T76-org/drpd/docs/docs/internals/interactive-diagram.mdx

---
sidebar_position: 1
slug: /internals/interactive-diagram/
hide_table_of_contents: true
title: Interactive diagram
description: Explore the Dr. PD R2605-A schematics in KiCanvas.
---

import InteractiveDiagram from '@site/src/components/InteractiveDiagram';

# Interactive diagram

Explore the R2605-A schematics in [KiCanvas](https://kicanvas.org/). Pan and zoom the diagram, select components, and use the project panel to move between schematic sheets.

<InteractiveDiagram />
