T76-org/drpd/frontend/src/content/initialNotice3.md

## Start using Dr. PD

That's it! If this is your first time using Dr. PD, the application will prompt you to pair your device as soon as you close this message.

There is no need to install any drivers or other software. Dr. PD runs entirely in your web browser, and all of your settings and log data are stored locally on your device. 

A [Python library](https://github.com/T76-org/drpd/tree/main/python) and terminal-based client are also available if you want to interact with Dr. PD programmatically.

To learn more about Dr. PD's features and how to use them, please read our [user guide](https://t76.org/drpd/docs/).
