T76-org/drpd/docs/docs/programming-guide/using-python-library/reference/package.mdx

---
sidebar_position: 50
sidebar_label: Package Entry Points
---

# Package Entry Points

:::info[Generated reference]
This page is generated from the Python source under `python/t76`. Do not edit it by hand; update source docstrings or the generator instead.
:::

Top-level package modules and command-line entry helpers.

## `t76`

**Source:** `python/t76/__init__.py`

Python tooling for T76.org devices.

No public classes or functions defined directly in this module.
