T76-org/drpd/hardware/R2605-A/kicad-schematics/Analog Monitor.kicad_sch

## KiCad design hardware/R2605-A/kicad-schematics/Analog Monitor.kicad_sch (2026-07-29)

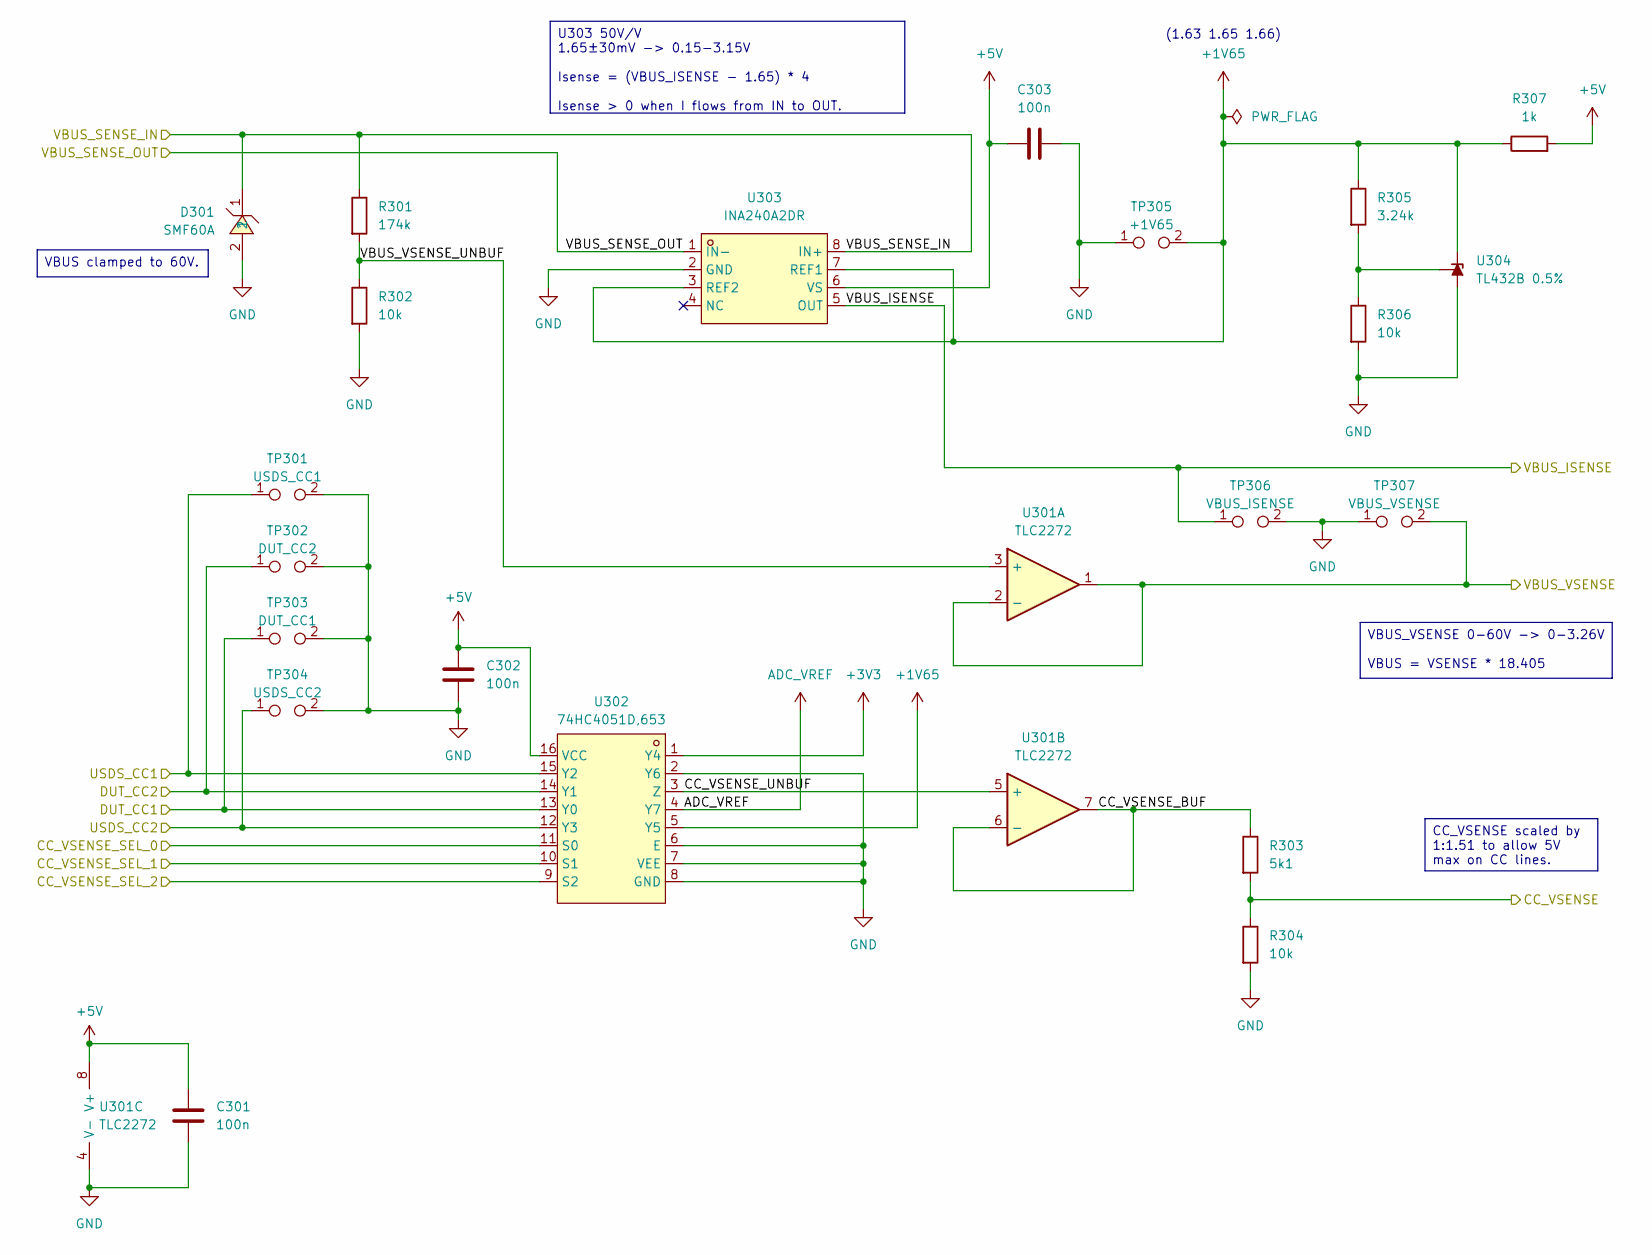
[picture p29: schematic Analog Monitor.kicad_sch]

Parts:
C301, C302, C303: 100n; C_1206_3216Metric; MPN C15008
D301: SMF60A; SOD-123FL_L2.8-W1.8-LS3.6-RD; LCSC Part C2857295
R301: 174k; R_1206_3216Metric; LCSC Part C274094
R302: 10k; R_1206_3216Metric; LCSC Part C17902
R303: 5k1; R_1206_3216Metric; MPN C26033
R304, R306: 10k; R_1206_3216Metric; MPN C17902
R305: 3.24k; R_1206_3216Metric; MPN C5153989
R307: 1k; R_1206_3216Metric; MPN C4410
TP301: USDS_CC1; TestPoint_2Pads_Pitch2.54mm_Drill0.8mm
TP302: DUT_CC2; TestPoint_2Pads_Pitch2.54mm_Drill0.8mm
TP303: DUT_CC1; TestPoint_2Pads_Pitch2.54mm_Drill0.8mm
TP304: USDS_CC2; TestPoint_2Pads_Pitch2.54mm_Drill0.8mm
TP305: +1V65; TestPoint_2Pads_Pitch2.54mm_Drill0.8mm
TP306: VBUS_ISENSE; TestPoint_2Pads_Pitch2.54mm_Drill0.8mm
TP307: VBUS_VSENSE; TestPoint_2Pads_Pitch2.54mm_Drill0.8mm
U301: TLC2272; SOIC-8_L4.9-W3.9-P1.27-LS6.0-BL; MPN C6979
U302: 74HC4051D,653; SOIC-16_L9.9-W3.9-P1.27-LS6.0-BL; LCSC Part C9386
U303: INA240A2DR; SOIC-8_L5.0-W4.0-P1.27-LS6.0-BL; LCSC Part C2060768
U304: TL432B 0.5%; SOT-23-3_L2.9-W1.3-P1.90-LS2.4-BR; LCSC Part C545558

Connections:
+1V65: R305.1, R307.1, TP305.2, U302.5 (Y5), U303.3 (REF2), U303.7 (REF1), U304.2 (K)
+3V3: U302.1 (Y4)
+5V: C301.1, C302.1, C303.1, R307.2, U301.8 (V+), U302.16 (VCC), U303.6 (VS)
ADC_VREF: U302.4 (Y7)
CC_VSENSE: R303.2, R304.1
CC_VSENSE_BUF: R303.1, U301.6 (-), U301.7
CC_VSENSE_SEL_0: U302.11 (S0)
CC_VSENSE_SEL_1: U302.10 (S1)
CC_VSENSE_SEL_2: U302.9 (S2)
CC_VSENSE_UNBUF: U301.5 (+), U302.3 (Z)
DUT_CC1: TP303.1, U302.13 (Y0)
DUT_CC2: TP302.1, U302.14 (Y1)
GND: C301.2, C302.2, C303.2, D301.2, R302.2, R304.2, R306.2, TP301.2, TP302.2, TP303.2, TP304.2, TP305.1, TP306.2, TP307.1, U301.4 (V-), U302.2 (Y6), U302.6 (E), U302.7 (VEE), U302.8 (GND), U303.2 (GND), U304.3 (A)
unnamed: R305.2, R306.1, U304.1 (REF)
USDS_CC1: TP301.1, U302.15 (Y2)
USDS_CC2: TP304.1, U302.12 (Y3)
VBUS_ISENSE: TP306.1, U303.5 (OUT)
VBUS_SENSE_IN: D301.1, R301.1, U303.8 (IN+)
VBUS_SENSE_OUT: U303.1 (IN-)
VBUS_VSENSE: TP307.2, U301.1, U301.2 (-)
VBUS_VSENSE_UNBUF: R301.2, R302.1, U301.3 (+)

Notes on the sheet:
(1.63 1.65 1.66)
VBUS clamped to 60V.
U303 50V/V 1.65±30mV -> 0.15-3.15V Isense = (VBUS_ISENSE - 1.65) * 4 Isense > 0 when I flows from IN to OUT.
CC_VSENSE scaled by 1:1.51 to allow 5V max on CC lines.
VBUS_VSENSE 0-60V -> 0-3.26V VBUS = VSENSE * 18.405
