T76-org/drpd/hardware/R2605-A/kicad-schematics/Bus Connector and Digital IO.kicad_sch

## KiCad design hardware/R2605-A/kicad-schematics/Bus Connector and Digital IO.kicad_sch (2026-07-29)

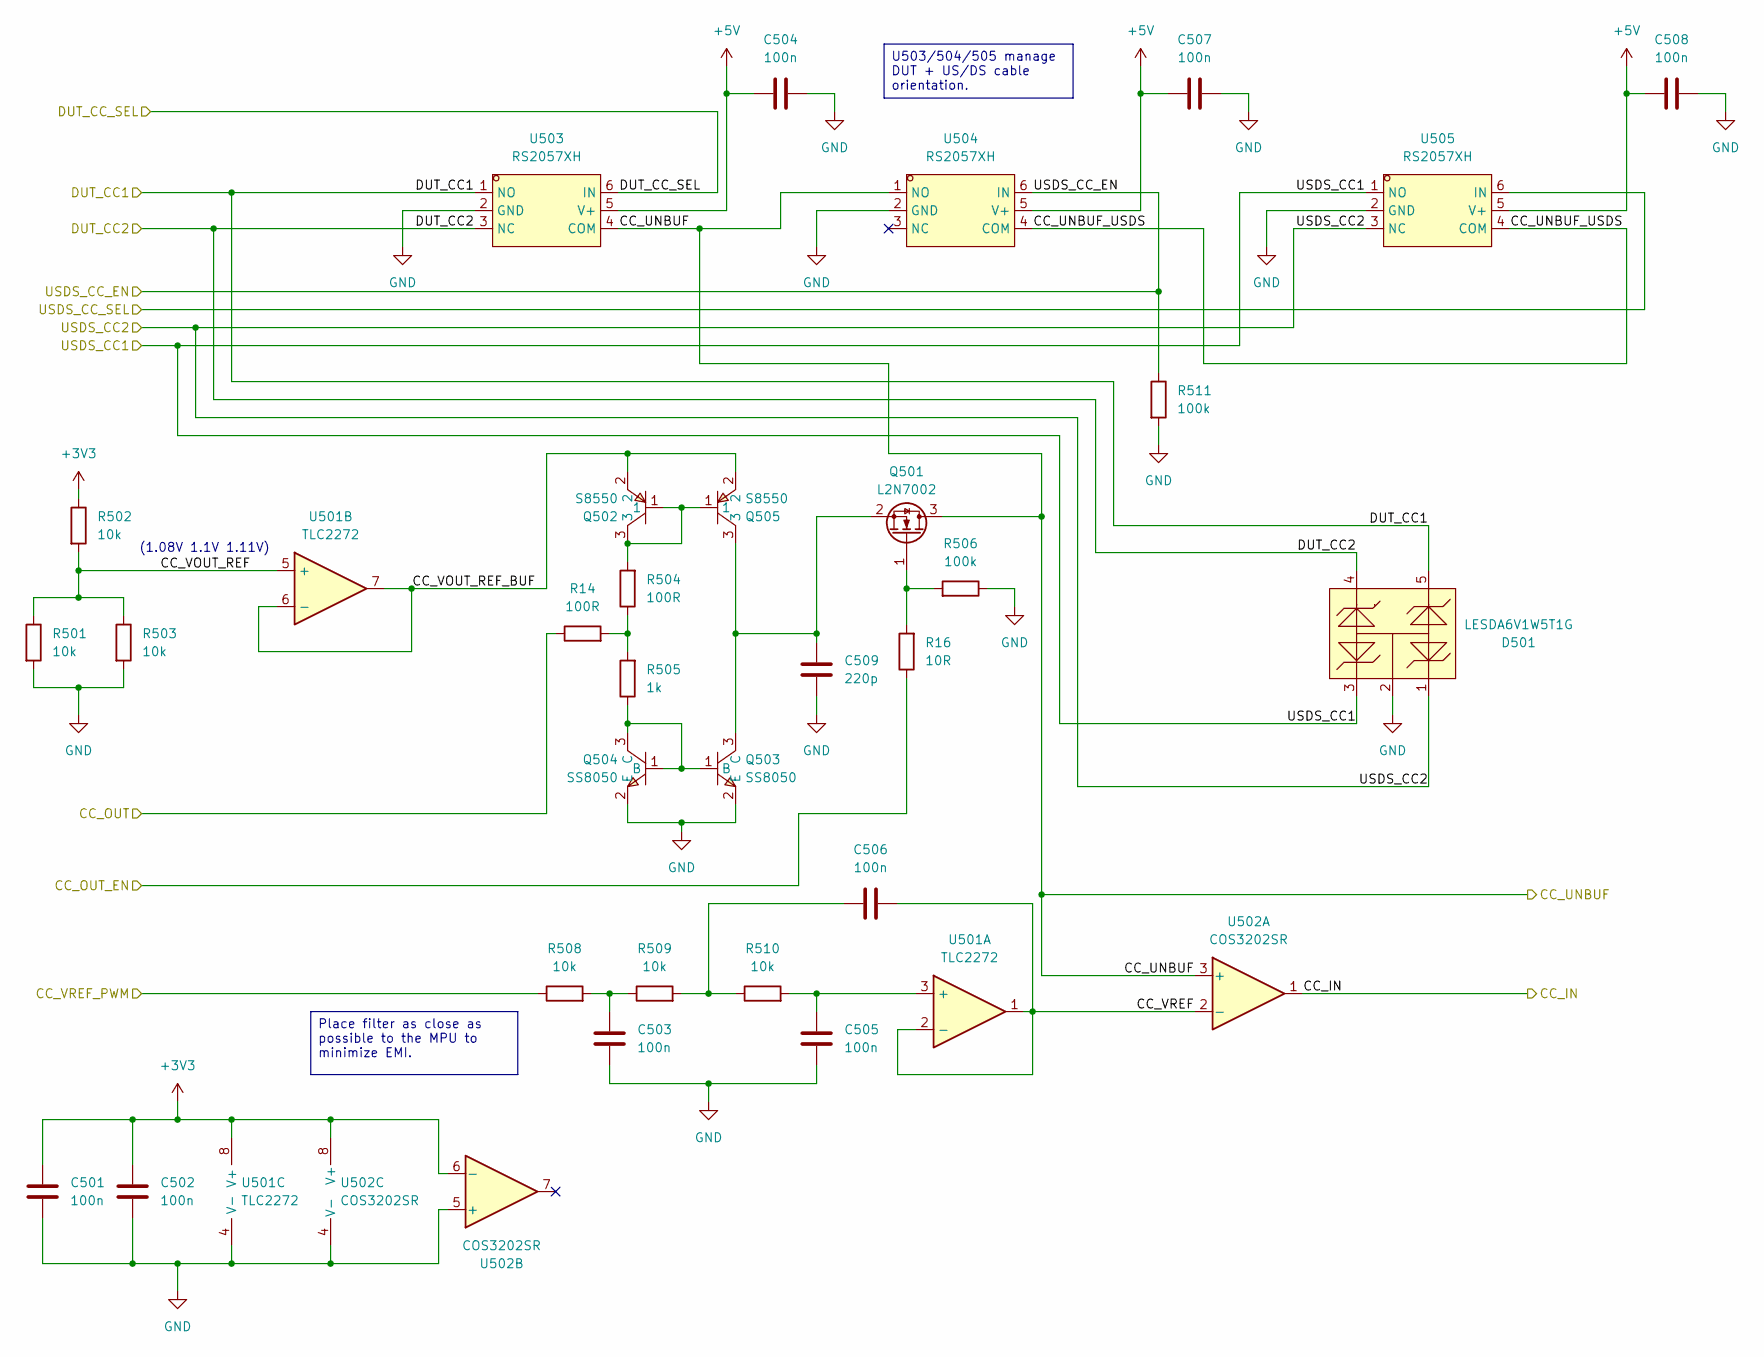
[picture p30: schematic Bus Connector and Digital IO.kicad_sch]

Parts:
C501, C502, C503, C504, C505, C506, C507, C508: 100n; C_1206_3216Metric; MPN C15008
C509: 220p; C_1206_3216Metric; MPN C107175
D501: LESDA6V1W5T1G; SC-88A_L2.0-W1.3-P0.65-LS2.1-BL-1; LCSC Part C383221
Q501: L2N7002; SOT-23-3_L3.0-W1.7-P0.95-LS2.9-BR; LCSC Part C22446827
Q502, Q505: S8550; SOT-23-3_L2.9-W1.6-P1.90-LS2.8-BR; MPN S8550(RANGE:120-200); LCSC Part C105432
Q503, Q504: SS8050; SOT-23-3_L2.9-W1.3-P1.90-LS2.4-BR; MPN SS8050(RANGE:200-350); LCSC Part C2150
R14, R504: 100R; R_1206_3216Metric; MPN C17901
R16: 10R; R_1206_3216Metric; MPN C17903
R501, R502, R503, R508, R509, R510: 10k; R_1206_3216Metric; MPN C17902
R505: 1k; R_1206_3216Metric; MPN C4410
R506, R511: 100k; R_1206_3216Metric; MPN C17900
U501: TLC2272; SOIC-8_L4.9-W3.9-P1.27-LS6.0-BL; MPN C6979
U502: COS3202SR; SOIC-8_L5.0-W4.0-P1.27-LS6.0-BL; MPN C49304671
U503, U504, U505: RS2057XH; SOT-23-6_L2.9-W1.6-P0.95-LS2.8-BR; LCSC Part C255474

Connections:
+3V3: C501.1, C502.1, R502.1, U501.8 (V+), U502.6 (-), U502.8 (V+)
+5V: C504.2, C507.2, C508.2, U503.5 (V+), U504.5 (V+), U505.5 (V+)
CC_IN: U502.1
CC_OUT: R14.1
CC_OUT_EN: R16.1
CC_UNBUF: Q501.3 (D), U502.3 (+), U503.4 (COM), U504.1 (NO)
CC_UNBUF_USDS: U504.4 (COM), U505.4 (COM)
CC_VOUT_REF: R501.1, R502.2, R503.1, U501.5 (+)
CC_VOUT_REF_BUF: Q502.2, Q505.2, U501.6 (-), U501.7
CC_VREF: C506.2, U501.1, U501.2 (-), U502.2 (-)
CC_VREF_PWM: R508.1
DUT_CC1: D501.5, U503.1 (NO)
DUT_CC2: D501.4, U503.3 (NC)
DUT_CC_SEL: U503.6 (IN)
GND: C501.2, C502.2, C503.2, C504.1, C505.2, C507.1, C508.1, C509.2, D501.2, Q503.2 (E), Q504.2 (E), R501.2, R503.2, R506.1, R511.2, U501.4 (V-), U502.4 (V-), U502.5 (+), U503.2 (GND), U504.2 (GND), U505.2 (GND)
unnamed: C503.1, R508.2, R509.1
unnamed: C505.1, R510.2, U501.3 (+)
unnamed: C506.1, R509.2, R510.1
unnamed: C509.1, Q501.2 (S), Q503.3 (C), Q505.3
unnamed: Q501.1 (G), R16.2, R506.2
unnamed: Q502.1, Q502.3, Q505.1, R504.2
unnamed: Q503.1 (B), Q504.1 (B), Q504.3 (C), R505.1
unnamed: R14.2, R504.1, R505.2
USDS_CC1: D501.3, U505.1 (NO)
USDS_CC2: D501.1, U505.3 (NC)
USDS_CC_EN: R511.1, U504.6 (IN)
USDS_CC_SEL: U505.6 (IN)

Notes on the sheet:
(1.08V 1.1V 1.11V)
Place filter as close as possible to the MPU to minimize EMI.
U503/504/505 manage DUT + US/DS cable orientation.
