T76-org/drpd/hardware/R2605-A/kicad-schematics/Digital Control.kicad_sch

## KiCad design hardware/R2605-A/kicad-schematics/Digital Control.kicad_sch (2026-07-29)

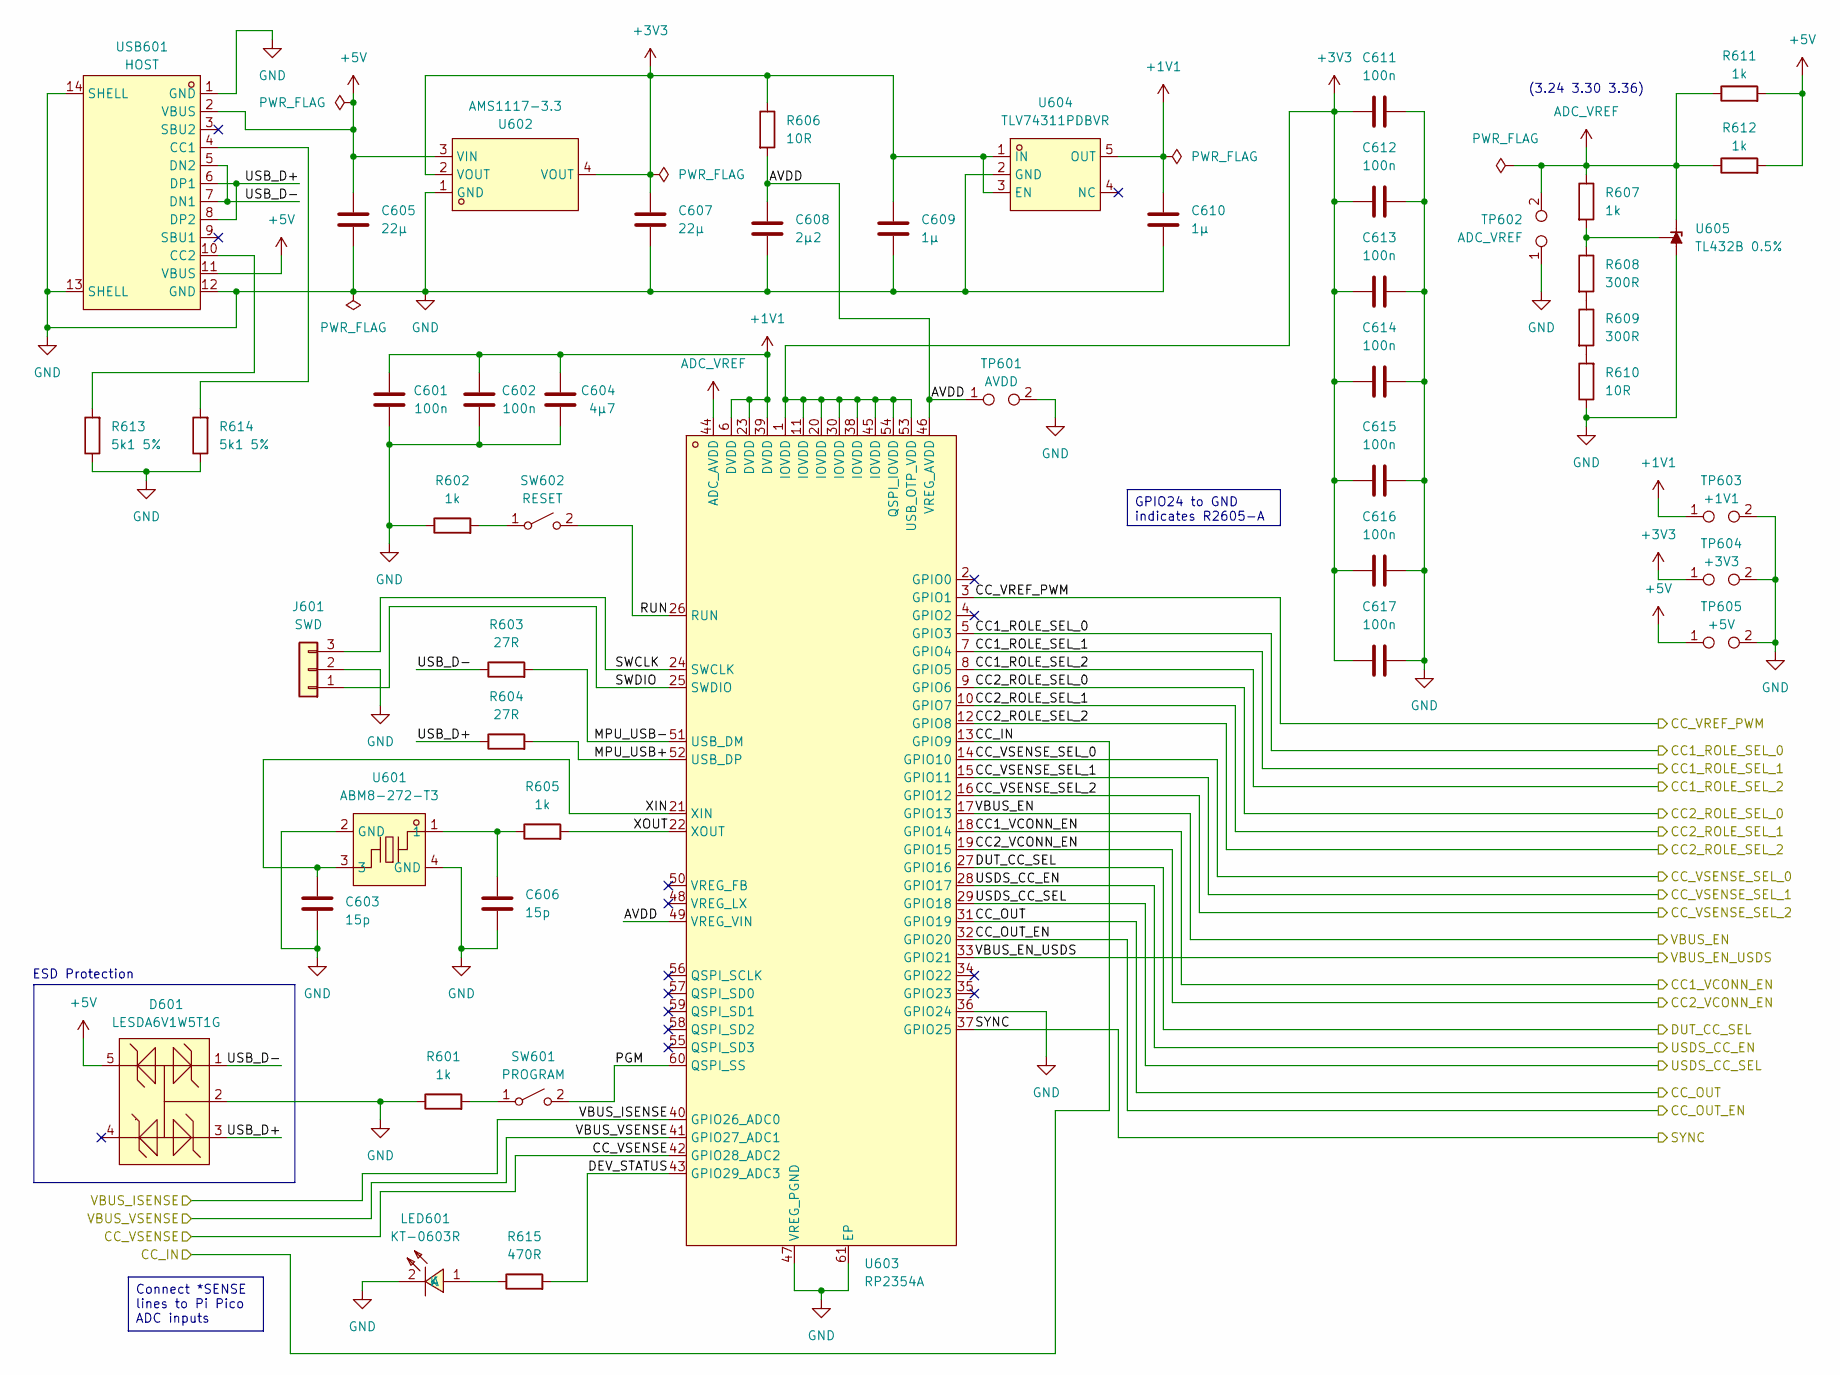
[picture p31: schematic Digital Control.kicad_sch]

Parts:
C601, C602, C611, C612, C613, C614, C615, C616, C617: 100n; C_1206_3216Metric; MPN C15008
C603, C606: 15p; C_1206_3216Metric; MPN C326650
C604: 4µ7; C_1206_3216Metric; MPN C29823
C605, C607: 22µ; C_1206_3216Metric; MPN C12891
C608: 2µ2; C_1206_3216Metric; MPN C50254
C609, C610: 1µ; C_1206_3216Metric; MPN C1848
D601: LESDA6V1W5T1G; SC-88A_L2.0-W1.3-P0.65-LS2.1-BL-1; LCSC Part C383221
J601: SWD; PinSocket_1x03_P2.54mm_Vertical
LED601: KT-0603R; LED-SMD_L1.6-W0.8-R-RD; MPN KT-0603R; LCSC Part C2286
R601, R602, R605, R607, R611, R612: 1k; R_1206_3216Metric; MPN C4410
R603, R604: 27R; R_1206_3216Metric; MPN C2933656
R606, R610: 10R; R_1206_3216Metric; MPN C17903
R608, R609: 300R; R_1206_3216Metric; MPN C17887
R613, R614: 5k1 5%; R_1206_3216Metric; MPN C2907509
R615: 470R; R_1206_3216Metric; MPN C185720
SW601: PROGRAM; SW-SMD_L3.9-W3.0-P4.45; MPN C720477
SW602: RESET; SW-SMD_L3.9-W3.0-P4.45; MPN C720477
TP601: AVDD; TestPoint_2Pads_Pitch2.54mm_Drill0.8mm
TP602: ADC_VREF; TestPoint_2Pads_Pitch2.54mm_Drill0.8mm
TP603: +1V1; TestPoint_2Pads_Pitch2.54mm_Drill0.8mm
TP604: +3V3; TestPoint_2Pads_Pitch2.54mm_Drill0.8mm
TP605: +5V; TestPoint_2Pads_Pitch2.54mm_Drill0.8mm
U601: ABM8-272-T3; CRYSTAL-SMD_4P-L3.2-W2.5-BL; LCSC Part C20625731
U602: AMS1117-3.3; SOT-223-3_L6.5-W3.4-P2.30-LS7.0-BR; LCSC Part C6186
U603: RP2354A; QFN-60_L7.0-W7.0-P0.40-TL-EP3.4; LCSC Part C41378174
U604: TLV74311PDBVR; SOT-23-5_L3.0-W1.7-P0.95-LS2.8-BL; LCSC Part C485147
U605: TL432B 0.5%; SOT-23-3_L2.9-W1.3-P1.90-LS2.4-BR; LCSC Part C545558
USB601: HOST; USB-C-SMD_TYPE-C-6PIN-2MD-073; LCSC Part C2765186

Connections:
+1V1: C601.1, C602.1, C604.1, C610.1, TP603.1, U603.6 (DVDD), U603.23 (DVDD), U603.39 (DVDD), U604.5 (OUT)
+3V3: C607.1, C609.1, C611.1, C612.1, C613.1, C614.1, C615.1, C616.1, C617.1, R606.1, TP604.1, U602.2 (VOUT), U602.4 (VOUT), U603.1 (IOVDD), U603.11 (IOVDD), U603.20 (IOVDD), U603.30 (IOVDD), U603.38 (IOVDD), U603.45 (IOVDD), U603.53 (USB_OTP_VDD), U603.54 (QSPI_IOVDD), U604.1 (IN), U604.3 (EN)
+5V: C605.1, D601.5, R611.2, R612.2, TP605.1, U602.3 (VIN), USB601.2 (VBUS), USB601.11 (VBUS)
ADC_VREF: R607.1, R611.1, R612.1, TP602.2, U603.44 (ADC_AVDD), U605.2 (K)
AVDD: C608.1, R606.2, TP601.1, U603.46 (VREG_AVDD), U603.49 (VREG_VIN)
CC1_ROLE_SEL_0: U603.5 (GPIO3)
CC1_ROLE_SEL_1: U603.7 (GPIO4)
CC1_ROLE_SEL_2: U603.8 (GPIO5)
CC1_VCONN_EN: U603.18 (GPIO14)
CC2_ROLE_SEL_0: U603.9 (GPIO6)
CC2_ROLE_SEL_1: U603.10 (GPIO7)
CC2_ROLE_SEL_2: U603.12 (GPIO8)
CC2_VCONN_EN: U603.19 (GPIO15)
CC_IN: U603.13 (GPIO9)
CC_OUT: U603.31 (GPIO19)
CC_OUT_EN: U603.32 (GPIO20)
CC_VREF_PWM: U603.3 (GPIO1)
CC_VSENSE: U603.42 (GPIO28_ADC2)
CC_VSENSE_SEL_0: U603.14 (GPIO10)
CC_VSENSE_SEL_1: U603.15 (GPIO11)
CC_VSENSE_SEL_2: U603.16 (GPIO12)
DEV_STATUS: R615.2, U603.43 (GPIO29_ADC3)
DUT_CC_SEL: U603.27 (GPIO16)
GND: C601.2, C602.2, C603.2, C604.2, C605.2, C606.2, C607.2, C608.2, C609.2, C610.2, C611.2, C612.2, C613.2, C614.2, C615.2, C616.2, C617.2, D601.2, J601.2, LED601.2 (K), R601.1, R602.1, R610.1, R613.1, R614.1, TP601.2, TP602.1, TP603.2, TP604.2, TP605.2, U601.2 (GND), U601.4 (GND), U602.1 (GND), U603.36 (GPIO24), U603.47 (VREG_PGND), U603.61 (EP), U604.2 (GND), U605.3 (A), USB601.1 (GND), USB601.12 (GND), USB601.13 (SHELL), USB601.14 (SHELL)
MPU_USB+: R604.2, U603.52 (USB_DP)
MPU_USB-: R603.2, U603.51 (USB_DM)
unnamed: C606.1, R605.1, U601.1
unnamed: LED601.1 (A), R615.1
unnamed: R601.2, SW601.1 (A)
unnamed: R602.2, SW602.1 (A)
unnamed: R607.2, R608.1, U605.1 (REF)
unnamed: R608.2, R609.1
unnamed: R609.2, R610.2
unnamed: R613.2, USB601.10 (CC2)
unnamed: R614.2, USB601.4 (CC1)
PGM: SW601.2 (B), U603.60 (QSPI_SS)
RUN: SW602.2 (B), U603.26 (RUN)
SWCLK: J601.3, U603.24 (SWCLK)
SWDIO: J601.1, U603.25 (SWDIO)
SYNC: U603.37 (GPIO25)
USB_D+: D601.3, R604.1, USB601.6 (DP1), USB601.8 (DP2)
USB_D-: D601.1, R603.1, USB601.5 (DN2), USB601.7 (DN1)
USDS_CC_EN: U603.28 (GPIO17)
USDS_CC_SEL: U603.29 (GPIO18)
VBUS_EN: U603.17 (GPIO13)
VBUS_EN_USDS: U603.33 (GPIO21)
VBUS_ISENSE: U603.40 (GPIO26_ADC0)
VBUS_VSENSE: U603.41 (GPIO27_ADC1)
XIN: C603.1, U601.3, U603.21 (XIN)
XOUT: R605.2, U603.22 (XOUT)

Notes on the sheet:
ESD Protection
(3.24 3.30 3.36)
GPIO24 to GND indicates R2605-A
Connect *SENSE lines to Pi Pico ADC inputs
