T76-org/drpd/hardware/R2605-A/kicad-schematics/Dr.PD.kicad_sch

## KiCad design hardware/R2605-A/kicad-schematics/Dr.PD.kicad_sch (2026-07-29)

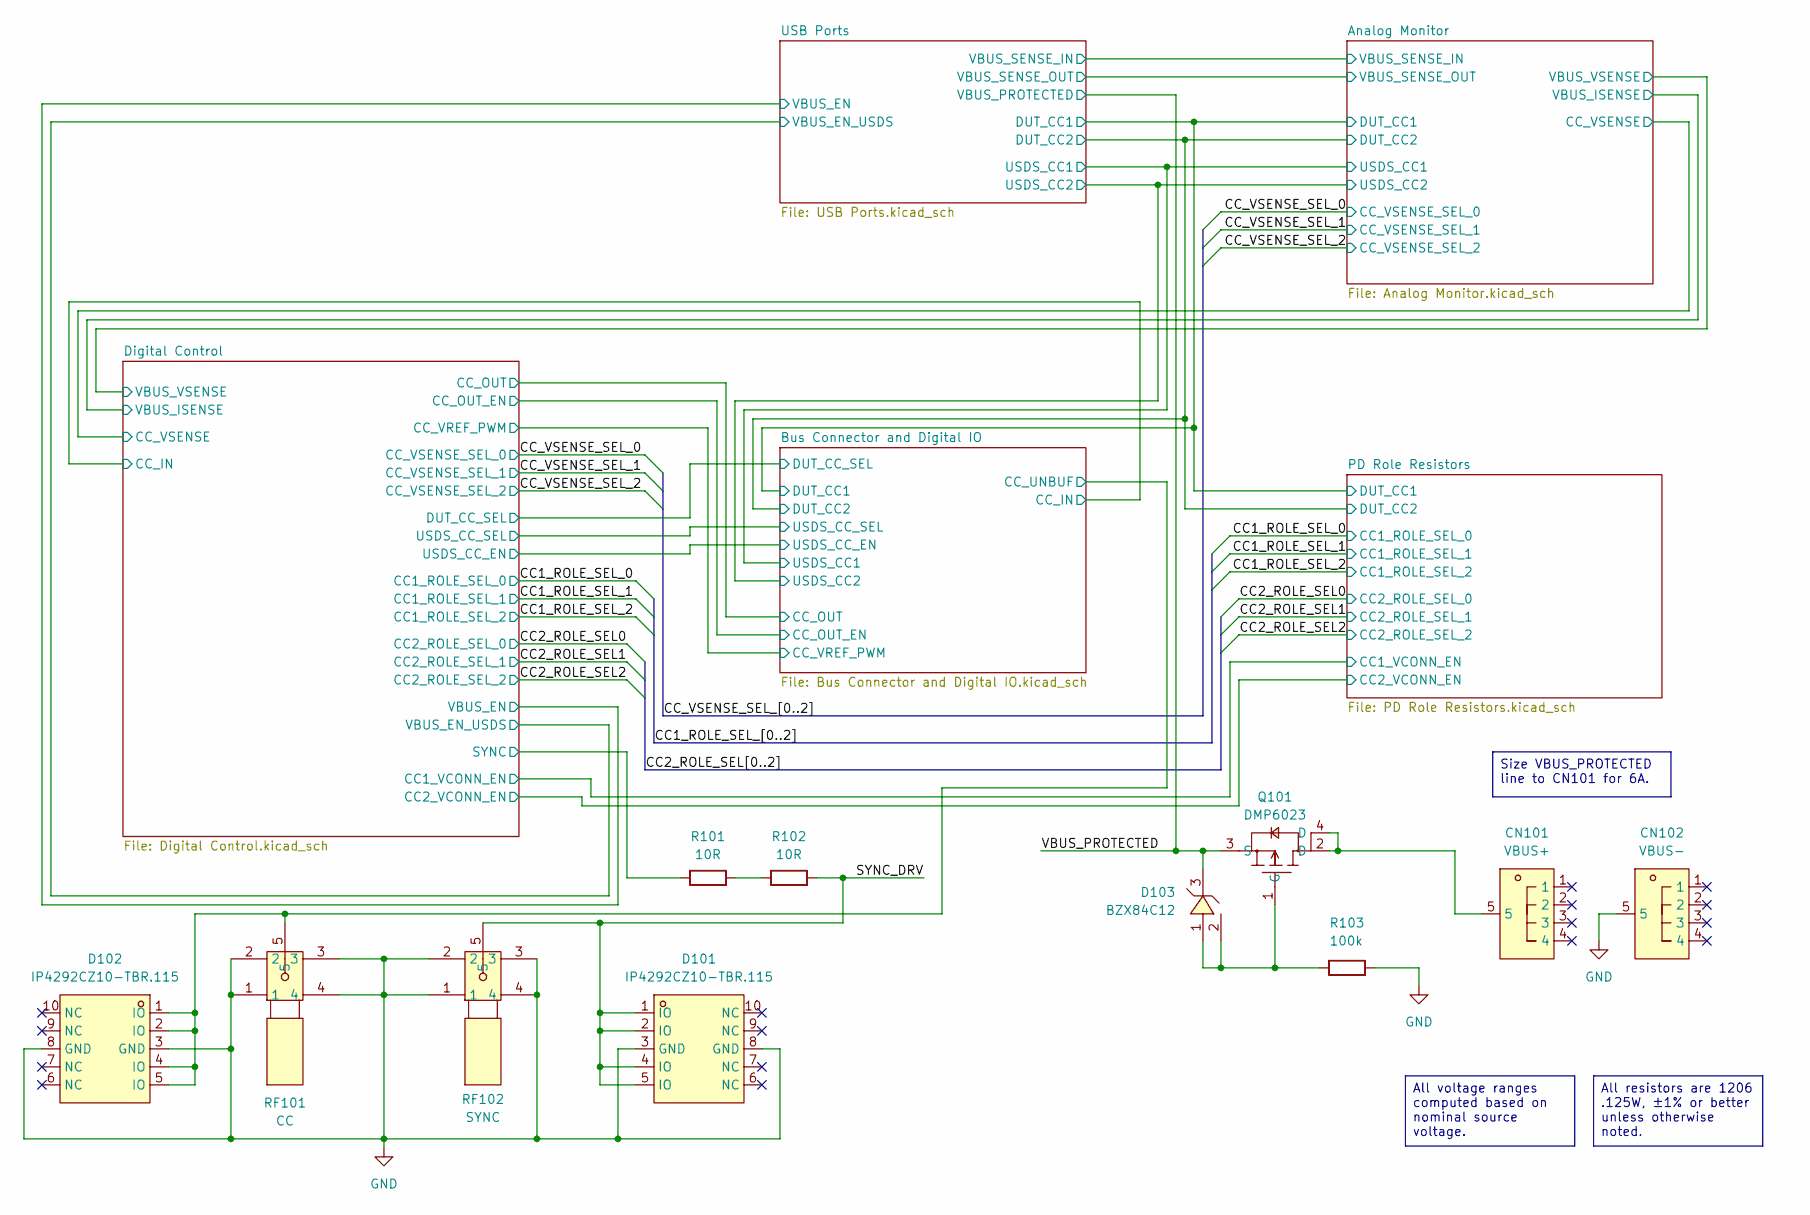
[picture p32: schematic Dr.PD.kicad_sch]

Parts:
CN101: VBUS+; ANT-TH_L33.0-W12.0_RED; LCSC Part C7437326
CN102: VBUS-; ANT-TH_L33.0-W12.0_BLACK; LCSC Part C7437327
D101, D102: IP4292CZ10-TBR.115; DFN2510A-10_L2.5-W1.0-P0.50-BL; LCSC Part C39832202
D103: BZX84C12; SOT-23_L2.9-W1.3-P1.90-LS2.4-BR; LCSC Part C19077471
Q101: DMP6023; SOT-223-4_L6.5-W3.5-P2.30-LS7.0-BR; LCSC Part C154901
R101, R102: 10R; R_1206_3216Metric; MPN C17903
R103: 100k; R_1206_3216Metric; MPN C17900
RF101: CC; BNC-TH_DOSIN-801-0051; LCSC Part C521210
RF102: SYNC; BNC-TH_DOSIN-801-0051; LCSC Part C521210

Connections:
CC_UNBUF: D102.1 (IO), D102.2 (IO), D102.4 (IO), D102.5 (IO), RF101.5
GND: CN102.5, D101.3 (GND), D101.8 (GND), D102.3 (GND), D102.8 (GND), R103.2, RF101.1, RF101.2, RF101.3, RF101.4, RF102.1, RF102.2, RF102.3, RF102.4
unnamed: CN101.5, Q101.2 (D), Q101.4 (D)
unnamed: D103.1, D103.2, Q101.1 (G), R103.1
unnamed: R101.2, R102.1
SYNC: R101.1
SYNC_DRV: D101.1 (IO), D101.2 (IO), D101.4 (IO), D101.5 (IO), R102.2, RF102.5
VBUS_PROTECTED: D103.3, Q101.3 (S)

Notes on the sheet:
Size VBUS_PROTECTED line to CN101 for 6A.
All voltage ranges computed based on nominal source voltage.
All resistors are 1206 .125W, ±1% or better unless otherwise noted.
