T76-org/drpd/hardware/R2605-A/kicad-schematics/PD Role Resistors.kicad_sch

## KiCad design hardware/R2605-A/kicad-schematics/PD Role Resistors.kicad_sch (2026-07-29)

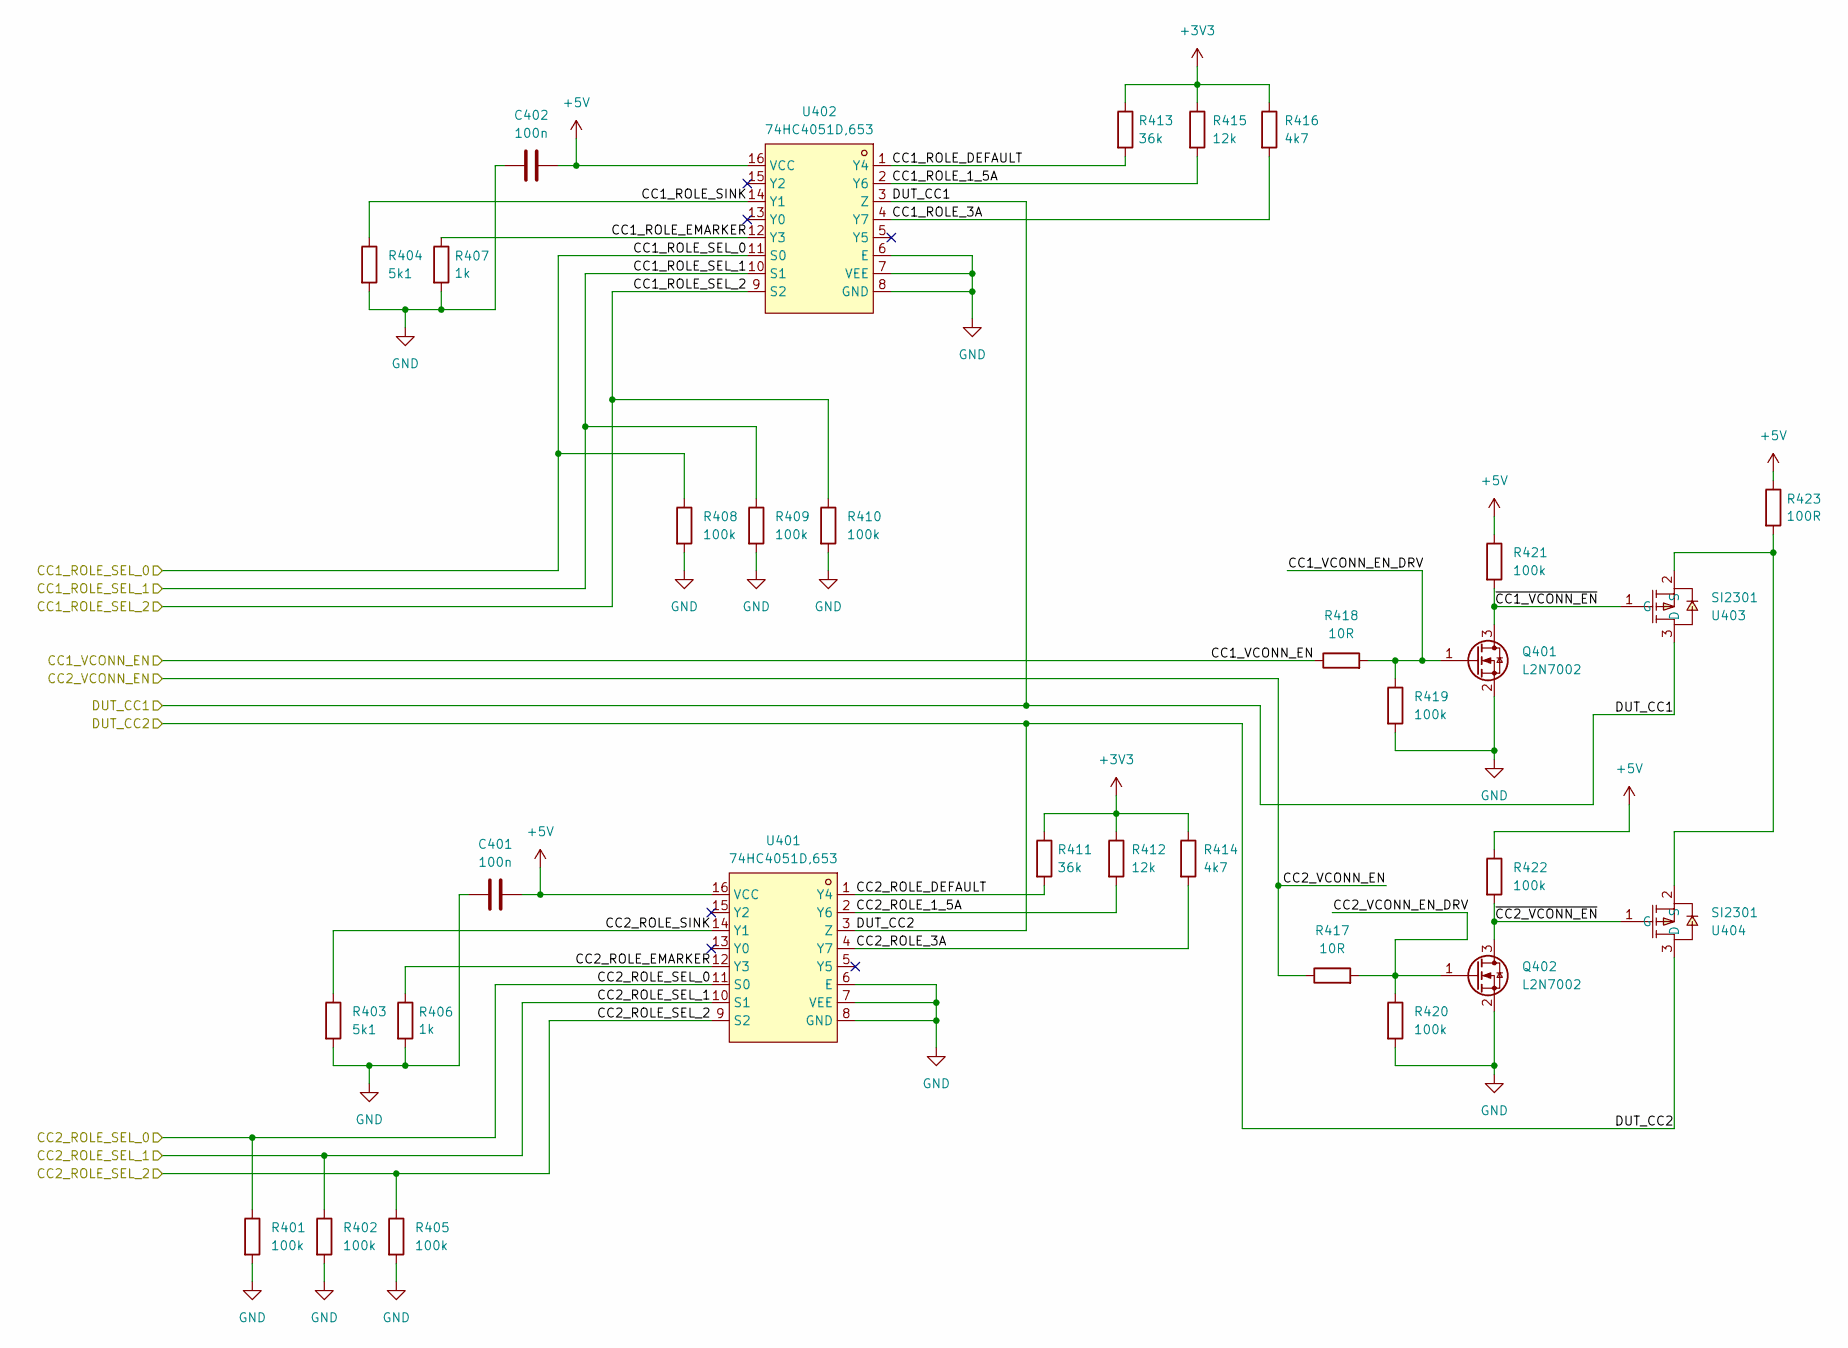
[picture p33: schematic PD Role Resistors.kicad_sch]

Parts:
C401, C402: 100n; C_1206_3216Metric; MPN C15008
Q401, Q402: L2N7002; SOT-23-3_L3.0-W1.7-P0.95-LS2.9-BR; LCSC Part C22446827
R401, R402, R405, R408, R409, R410, R419, R420, R421, R422: 100k; R_1206_3216Metric; MPN C17900
R403, R404: 5k1; R_1206_3216Metric; MPN C26033
R406, R407: 1k; R_1206_3216Metric; MPN C4410
R411, R413: 36k; R_1206_3216Metric; MPN C2933685
R412, R415: 12k; R_1206_3216Metric; MPN C17912
R414, R416: 4k7; R_1206_3216Metric; MPN C17936
R417, R418: 10R; R_1206_3216Metric; MPN C17903
R423: 100R; R_1206_3216Metric; MPN C17901
U401, U402: 74HC4051D,653; SOIC-16_L9.9-W3.9-P1.27-LS6.0-BL; LCSC Part C9386
U403, U404: SI2301; SOT-23-3_L2.9-W1.3-P1.90-LS2.4-BR; LCSC Part C5261052

Connections:
+3V3: R411.1, R412.1, R413.1, R414.1, R415.1, R416.1
+5V: C401.2, C402.2, R421.1, R422.1, R423.1, U401.16 (VCC), U402.16 (VCC)
CC1_ROLE_1_5A: R415.2, U402.2 (Y6)
CC1_ROLE_3A: R416.2, U402.4 (Y7)
CC1_ROLE_DEFAULT: R413.2, U402.1 (Y4)
CC1_ROLE_EMARKER: R407.1, U402.12 (Y3)
CC1_ROLE_SEL_0: R408.1, U402.11 (S0)
CC1_ROLE_SEL_1: R409.1, U402.10 (S1)
CC1_ROLE_SEL_2: R410.1, U402.9 (S2)
CC1_ROLE_SINK: R404.1, U402.14 (Y1)
CC1_VCONN_EN: R418.1
CC1_VCONN_EN_DRV: Q401.1 (G), R418.2, R419.1
CC2_ROLE_1_5A: R412.2, U401.2 (Y6)
CC2_ROLE_3A: R414.2, U401.4 (Y7)
CC2_ROLE_DEFAULT: R411.2, U401.1 (Y4)
CC2_ROLE_EMARKER: R406.1, U401.12 (Y3)
CC2_ROLE_SEL_0: R401.1, U401.11 (S0)
CC2_ROLE_SEL_1: R402.1, U401.10 (S1)
CC2_ROLE_SEL_2: R405.1, U401.9 (S2)
CC2_ROLE_SINK: R403.1, U401.14 (Y1)
CC2_VCONN_EN: R417.1
CC2_VCONN_EN_DRV: Q402.1 (G), R417.2, R420.1
DUT_CC1: U402.3 (Z), U403.3 (D)
DUT_CC2: U401.3 (Z), U404.3 (D)
GND: C401.1, C402.1, Q401.2 (S), Q402.2 (S), R401.2, R402.2, R403.2, R404.2, R405.2, R406.2, R407.2, R408.2, R409.2, R410.2, R419.2, R420.2, U401.6 (E), U401.7 (VEE), U401.8 (GND), U402.6 (E), U402.7 (VEE), U402.8 (GND)
unnamed: R423.2, U403.2 (S), U404.2 (S)
~CC1_VCONN_EN: Q401.3 (D), R421.2, U403.1 (G)
~CC2_VCONN_EN: Q402.3 (D), R422.2, U404.1 (G)
