T76-org/drpd/hardware/R2605-A/kicad-schematics/USB Ports.kicad_sch

## KiCad design hardware/R2605-A/kicad-schematics/USB Ports.kicad_sch (2026-07-29)

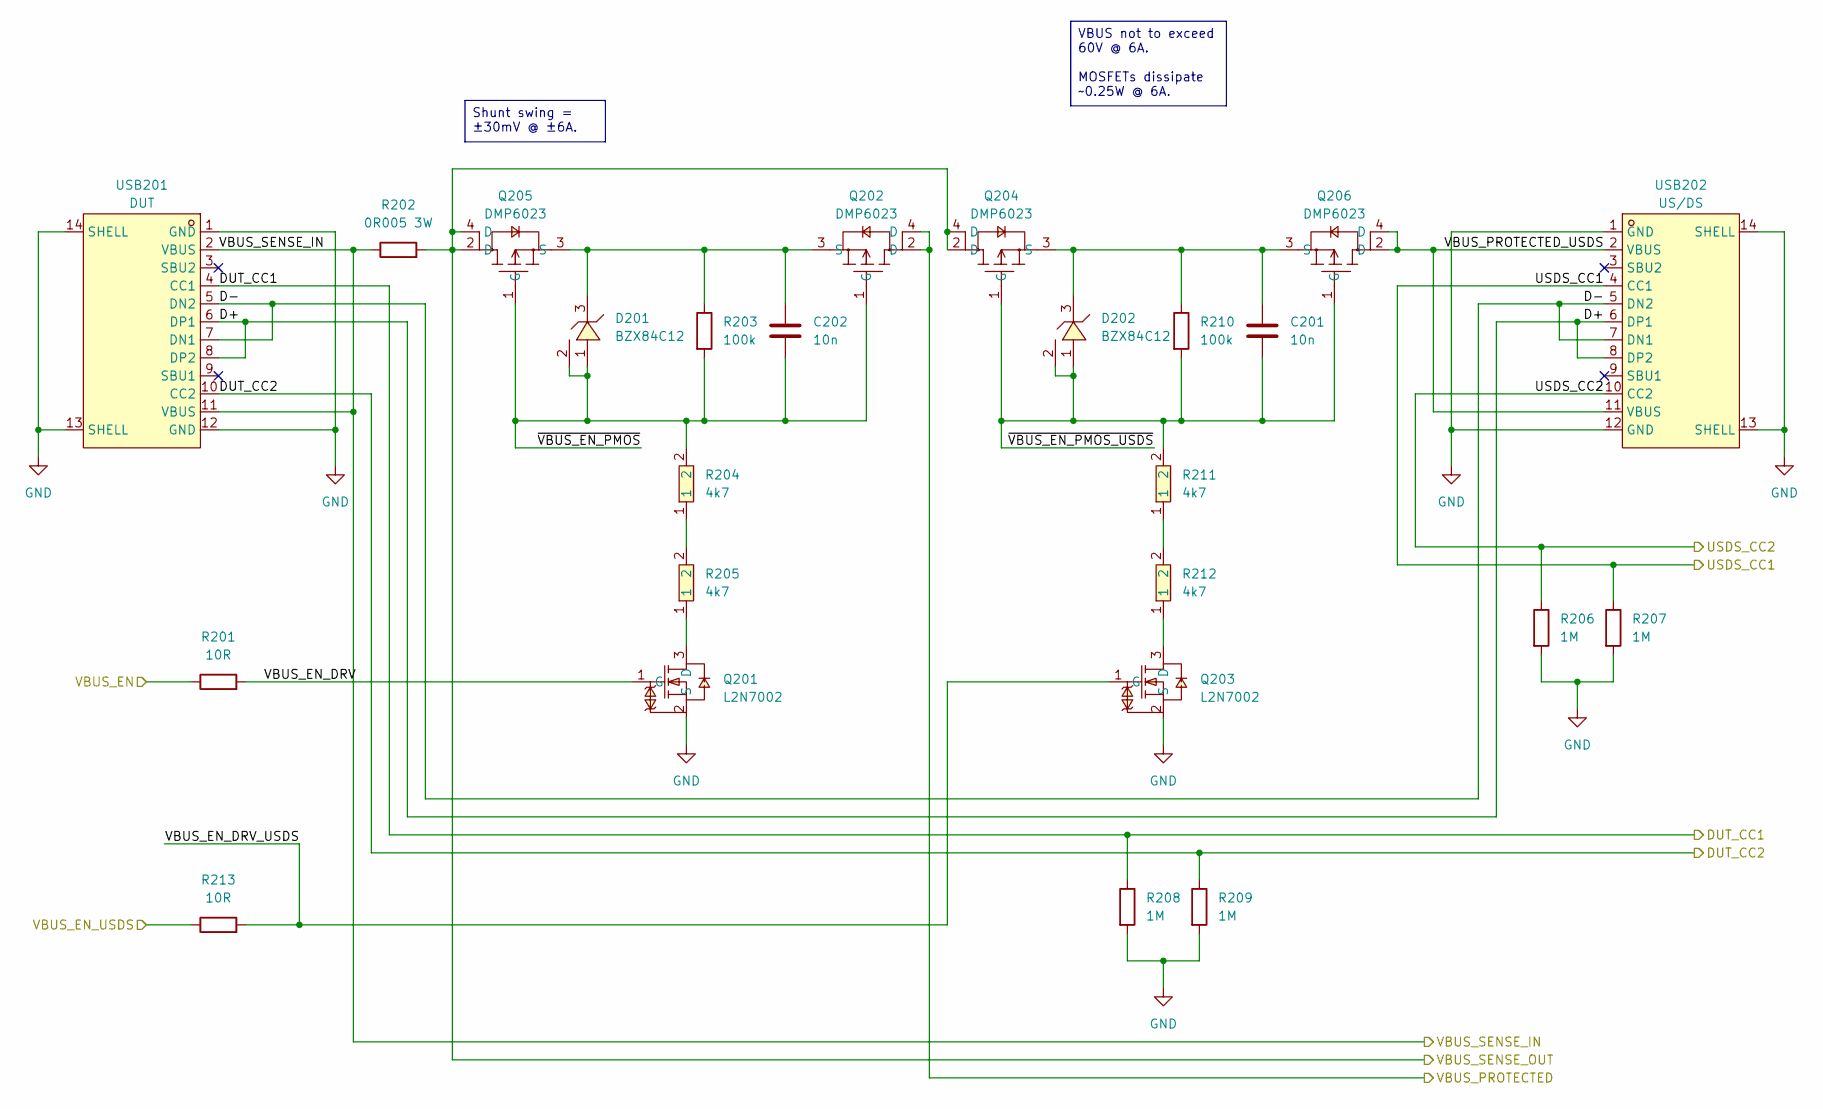
[picture p34: schematic USB Ports.kicad_sch]

Parts:
C201, C202: 10n; C_1206_3216Metric; MPN C1846
D201, D202: BZX84C12; SOT-23_L2.9-W1.3-P1.90-LS2.4-BR; LCSC Part C19077471
Q201, Q203: L2N7002; SOT-23-3_L3.0-W1.7-P0.95-LS2.9-BR; LCSC Part C22446827
Q202, Q204, Q205, Q206: DMP6023; SOT-223-4_L6.5-W3.5-P2.30-LS7.0-BR; LCSC Part C154901
R201, R213: 10R; R_1206_3216Metric; MPN C17903
R202: 0R005 3W; R_2512_6332Metric; LCSC Part C46634460
R203, R210: 100k; R_1206_3216Metric; MPN C17900
R204, R205, R211, R212: 4k7; R_1206_3216Metric; LCSC Part C17936
R206, R207, R208, R209: 1M; R_1206_3216Metric; MPN C17927
USB201: DUT; USB-C-SMD_TYPE-C-6PIN-2MD-073; LCSC Part C2765186
USB202: US/DS; USB-C-SMD_TYPE-C-6PIN-2MD-073; LCSC Part C2765186

Connections:
D+: USB201.6 (DP1), USB201.8 (DP2), USB202.6 (DP1), USB202.8 (DP2)
D-: USB201.5 (DN2), USB201.7 (DN1), USB202.5 (DN2), USB202.7 (DN1)
DUT_CC1: R208.1, USB201.4 (CC1)
DUT_CC2: R209.1, USB201.10 (CC2)
GND: Q201.2 (S), Q203.2 (S), R206.2, R207.2, R208.2, R209.2, USB201.1 (GND), USB201.12 (GND), USB201.13 (SHELL), USB201.14 (SHELL), USB202.1 (GND), USB202.12 (GND), USB202.13 (SHELL), USB202.14 (SHELL)
unnamed: C201.1, D202.3, Q204.3 (S), Q206.3 (S), R210.1
unnamed: C202.1, D201.3, Q202.3 (S), Q205.3 (S), R203.1
unnamed: Q201.3 (D), R205.1
unnamed: Q203.3 (D), R212.1
unnamed: R204.1, R205.2
unnamed: R211.1, R212.2
USDS_CC1: R207.1, USB202.4 (CC1)
USDS_CC2: R206.1, USB202.10 (CC2)
VBUS_EN: R201.1
VBUS_EN_DRV: Q201.1 (G), R201.2
VBUS_EN_DRV_USDS: Q203.1 (G), R213.2
VBUS_EN_USDS: R213.1
VBUS_PROTECTED: Q202.2 (D), Q202.4 (D)
VBUS_PROTECTED_USDS: Q206.2 (D), Q206.4 (D), USB202.2 (VBUS), USB202.11 (VBUS)
VBUS_SENSE_IN: R202.1, USB201.2 (VBUS), USB201.11 (VBUS)
VBUS_SENSE_OUT: Q204.2 (D), Q204.4 (D), Q205.2 (D), Q205.4 (D), R202.2
~VBUS_EN_PMOS_USDS: C201.2, D202.1, D202.2, Q204.1 (G), Q206.1 (G), R210.2, R211.2
~VBUS_EN_PMOS: C202.2, D201.1, D201.2, Q202.1 (G), Q205.1 (G), R203.2, R204.2

Notes on the sheet:
VBUS not to exceed 60V @ 6A. MOSFETs dissipate ~0.25W @ 6A.
Shunt swing = ±30mV @ ±6A.
